sparkfun/VKey_Voltage_Keypad/documents/VKey.asc

D2: diode; 1N914
Q1: pnp; 2N4403
R1: res; 330
R2: res; 330
R3: res; 330
R4: res; 330
R5: res; 330
R6: res; 330
R7: res; 330
R8: res; 330
R9: res; 330
R10: res; 330
R11: res; 1meg
R12: res; 1000
R13: res; 10k
R15: res; 330
R16: res; 330
U1: UniversalOpamp2
U2: UniversalOpamp2
V1: voltage; 5
Named nets: 0, VCC, Vbus, Vout
.tran 0 1 0
