sparkfun/VKey_Voltage_Keypad/documents/pictures/pic1.sch

## EAGLE design documents/pictures/pic1.sch (2014-02-14)

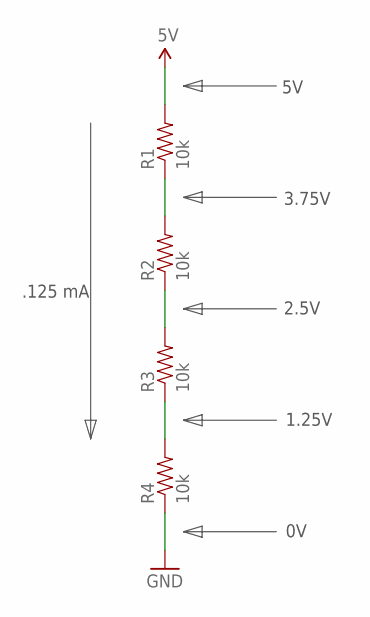
[picture p15: schematic pic1.sch]

Parts:
R1, R2, R3, R4: 10k; 0603-RES

Connections:
5V: R1.2
GND: R4.1
unnamed: R2.1, R3.2
unnamed: R1.1, R2.2
unnamed: R3.1, R4.2

Notes on the sheet:
3.75V
2.5V
1.25V
.125 mA
