sparkfun/VKey_Voltage_Keypad/documents/pictures/pic2.sch

## EAGLE design documents/pictures/pic2.sch (2014-02-14)

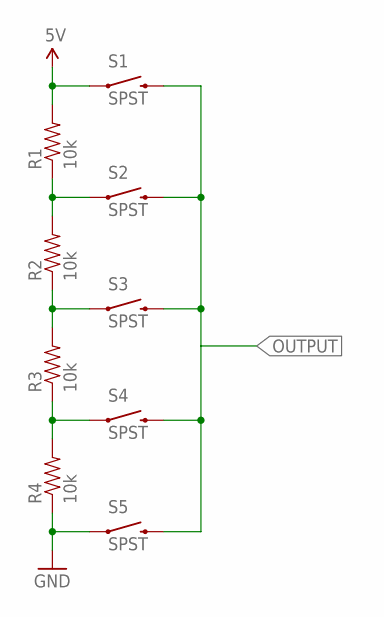
[picture p16: schematic pic2.sch]

Parts:
R1, R2, R3, R4: 10k; 0603-RES
S1, S2, S3, S4, S5: SPST; TACTILE-PTH-12MM

Connections:
5V: R1.2, S1.1
GND: R4.1, S5.1
unnamed: R2.1, R3.2, S3.1
unnamed: R1.1, R2.2, S2.1
unnamed: R3.1, R4.2, S4.1
OUTPUT: S1.3 (2), S2.3 (2), S3.3 (2), S4.3 (2), S5.3 (2)
